tewtham/dactyl-typesafe/things/4x6-wireless/wiring.jpg

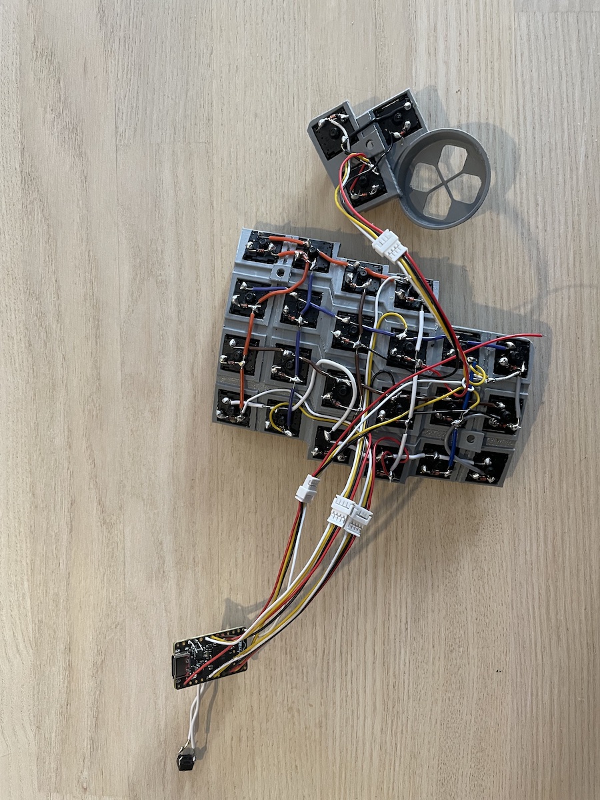
things/4x6-wireless/wiring.jpg
